jabadiagm/MSXhdmi_tn20k/fpga/impl/gwsynthesis/RTL_GAO/gw_gao_top.v

module gw_gao(
    ex_bus_sltsl_n,
    ex_bus_data_reverse_n,
    fmrom_read,
    ex_led,
    busReset_n,
    bus_sltsl_n,
    busMreq_n,
    bus_data_reverse,
    \fmrom_state[1] ,
    \fmrom_state[0] ,
    \fmrom_counter[4] ,
    \fmrom_counter[3] ,
    \fmrom_counter[2] ,
    \fmrom_counter[1] ,
    \fmrom_counter[0] ,
    ex_clk_27m,
    tms_pad_i,
    tck_pad_i,
    tdi_pad_i,
    tdo_pad_o
);

input ex_bus_sltsl_n;
input ex_bus_data_reverse_n;
input fmrom_read;
input ex_led;
input busReset_n;
input bus_sltsl_n;
input busMreq_n;
input bus_data_reverse;
input \fmrom_state[1] ;
input \fmrom_state[0] ;
input \fmrom_counter[4] ;
input \fmrom_counter[3] ;
input \fmrom_counter[2] ;
input \fmrom_counter[1] ;
input \fmrom_counter[0] ;
input ex_clk_27m;
input tms_pad_i;
input tck_pad_i;
input tdi_pad_i;
output tdo_pad_o;

wire ex_bus_sltsl_n;
wire ex_bus_data_reverse_n;
wire fmrom_read;
wire ex_led;
wire busReset_n;
wire bus_sltsl_n;
wire busMreq_n;
wire bus_data_reverse;
wire \fmrom_state[1] ;
wire \fmrom_state[0] ;
wire \fmrom_counter[4] ;
wire \fmrom_counter[3] ;
wire \fmrom_counter[2] ;
wire \fmrom_counter[1] ;
wire \fmrom_counter[0] ;
wire ex_clk_27m;
wire tms_pad_i;
wire tck_pad_i;
wire tdi_pad_i;
wire tdo_pad_o;
wire tms_i_c;
wire tck_i_c;
wire tdi_i_c;
wire tdo_o_c;
wire [9:0] control0;
wire gao_jtag_tck;
wire gao_jtag_reset;
wire run_test_idle_er1;
wire run_test_idle_er2;
wire shift_dr_capture_dr;
wire update_dr;
wire pause_dr;
wire enable_er1;
wire enable_er2;
wire gao_jtag_tdi;
wire tdo_er1;

IBUF tms_ibuf (
    .I(tms_pad_i),
    .O(tms_i_c)
);

IBUF tck_ibuf (
    .I(tck_pad_i),
    .O(tck_i_c)
);

IBUF tdi_ibuf (
    .I(tdi_pad_i),
    .O(tdi_i_c)
);

OBUF tdo_obuf (
    .I(tdo_o_c),
    .O(tdo_pad_o)
);

GW_JTAG  u_gw_jtag(
    .tms_pad_i(tms_i_c),
    .tck_pad_i(tck_i_c),
    .tdi_pad_i(tdi_i_c),
    .tdo_pad_o(tdo_o_c),
    .tck_o(gao_jtag_tck),
    .test_logic_reset_o(gao_jtag_reset),
    .run_test_idle_er1_o(run_test_idle_er1),
    .run_test_idle_er2_o(run_test_idle_er2),
    .shift_dr_capture_dr_o(shift_dr_capture_dr),
    .update_dr_o(update_dr),
    .pause_dr_o(pause_dr),
    .enable_er1_o(enable_er1),
    .enable_er2_o(enable_er2),
    .tdi_o(gao_jtag_tdi),
    .tdo_er1_i(tdo_er1),
    .tdo_er2_i(1'b0)
);

gw_con_top  u_icon_top(
    .tck_i(gao_jtag_tck),
    .tdi_i(gao_jtag_tdi),
    .tdo_o(tdo_er1),
    .rst_i(gao_jtag_reset),
    .control0(control0[9:0]),
    .enable_i(enable_er1),
    .shift_dr_capture_dr_i(shift_dr_capture_dr),
    .update_dr_i(update_dr)
);

ao_top_0  u_la0_top(
    .control(control0[9:0]),
    .trig0_i(ex_bus_sltsl_n),
    .data_i({ex_bus_sltsl_n,ex_bus_data_reverse_n,fmrom_read,ex_led,busReset_n,bus_sltsl_n,busMreq_n,bus_data_reverse,\fmrom_state[1] ,\fmrom_state[0] ,\fmrom_counter[4] ,\fmrom_counter[3] ,\fmrom_counter[2] ,\fmrom_counter[1] ,\fmrom_counter[0] }),
    .clk_i(ex_clk_27m)
);

endmodule
