jabadiagm/MSXhdmi_tn20k/fpga/src/fmrom.v

module fmrom(
    input [13:0] address,
    input clock,
    input [7:0] data,
    input wren,
    output [7:0] q
);

    reg [7:0] mem_r[0:16383];
    reg [7:0] q_r;

initial begin
    $readmemh("16k_fm_opl.bin.hex", mem_r);
end

    always @(posedge clock) begin
    
        q_r <= mem_r[address];

        if (wren == 1) begin
            mem_r[address] <= data;
        end

    end

    assign q = q_r;

endmodule
